badjeff/olliebella/STLs/controller clip.stl

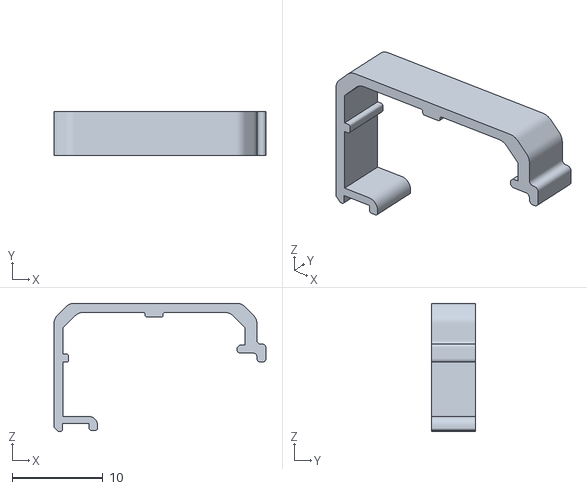
[picture p25: CAD file, 2026-09-13]
STLs/controller clip.stl
23.3 x 4.86 x 14.1
