badjeff/olliebella/STLs/m2.stl

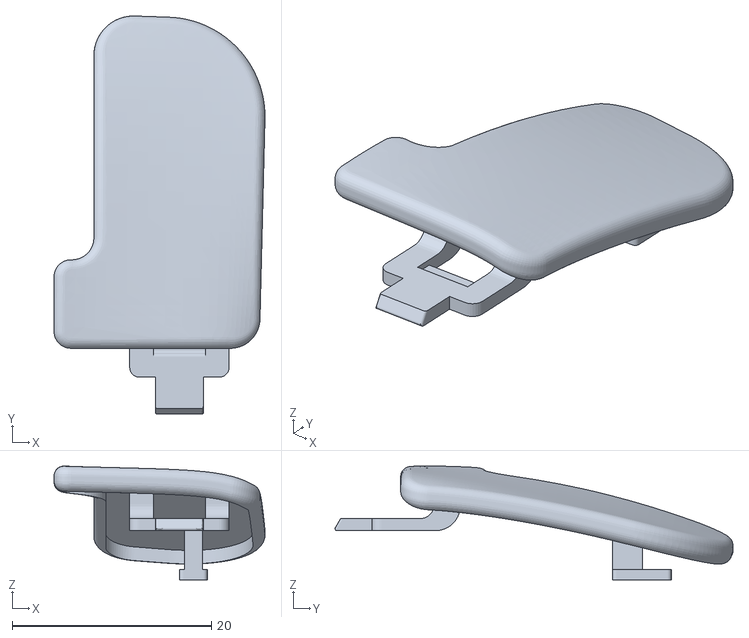
[picture p26: CAD file, 2026-09-13]
STLs/m2.stl
21.2 x 40.0 x 11.4
