badjeff/olliebella/STLs/m1 mount.stl

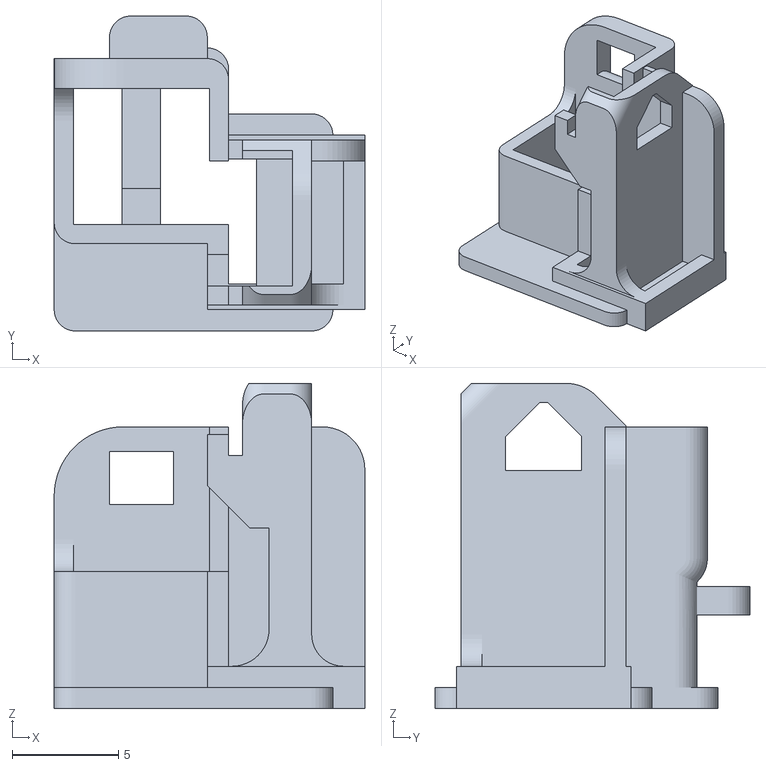
[picture p27: CAD file, 2026-09-13]
STLs/m1 mount.stl
14.6 x 14.8 x 15.3
