badjeff/olliebella/STLs/ps mount.stl

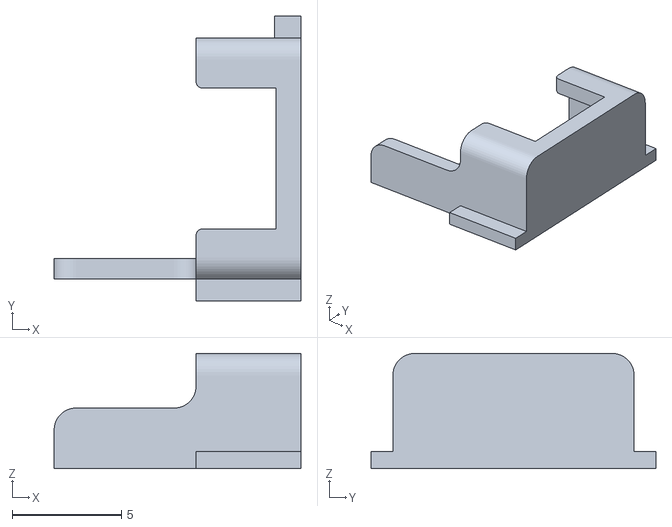
[picture p28: CAD file, 2026-09-13]
STLs/ps mount.stl
11.3 x 13.1 x 5.27
