badjeff/olliebella/STLs/shell (extended).stl

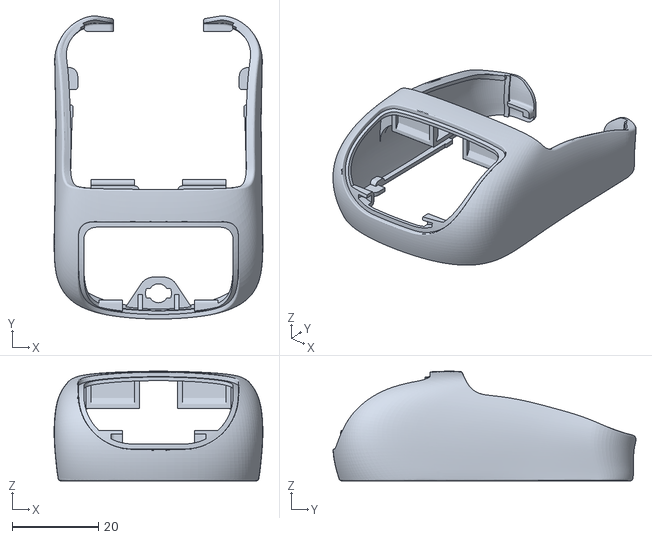
[picture p29: CAD file, 2026-09-13]
STLs/shell (extended).stl
48.3 x 70.2 x 25.4
