badjeff/olliebella/STLs/controller ring.stl

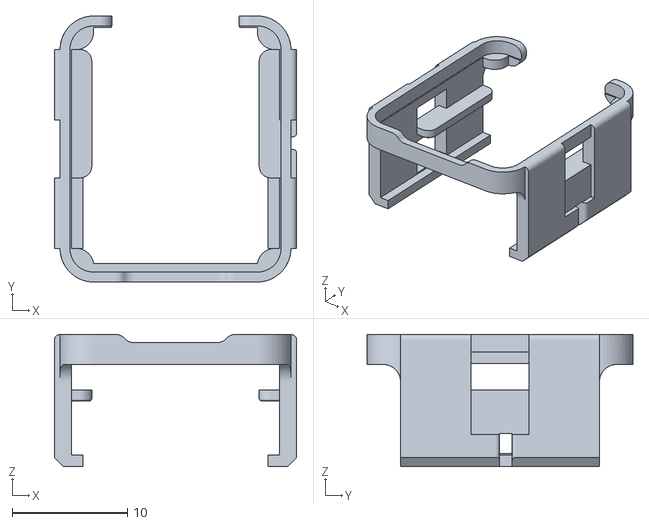
[picture p30: CAD file, 2026-09-13]
STLs/controller ring.stl
21.0 x 23.0 x 11.4
